COSMIIC-Inc/Implantables-Electrodes/Mechanical Design CAD Files/IM-MES Electrode Cable/SolidWorks Native Files/NNP-DWG-145-007-003 SA, Cable Body, Insulated SS Filars, Green-Clear.SLDASM

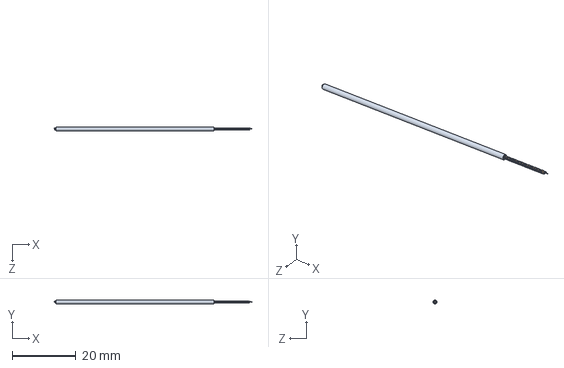
[picture p4: CAD file, 2024-06-29]
Mechanical Design CAD Files/IM-MES Electrode Cable/SolidWorks Native Files/NNP-DWG-145-007-003 SA, Cable Body, Insulated SS Filars, Green-Clear.SLDASM
62.2 x 1.27 x 1.27 mm
NNP-DWG-140-011-002 Filar, SS, Green-Clear
NNP-DWG-140-012-000 Cable, Insulating Silicone Tubing
