COSMIIC-Inc/Implantables-Electrodes/Mechanical Design CAD Files/IM Stim Electrode Cable/STEP Files/NNP-DWG-145-012-000 SA, Electrode, IM, Stim.STEP

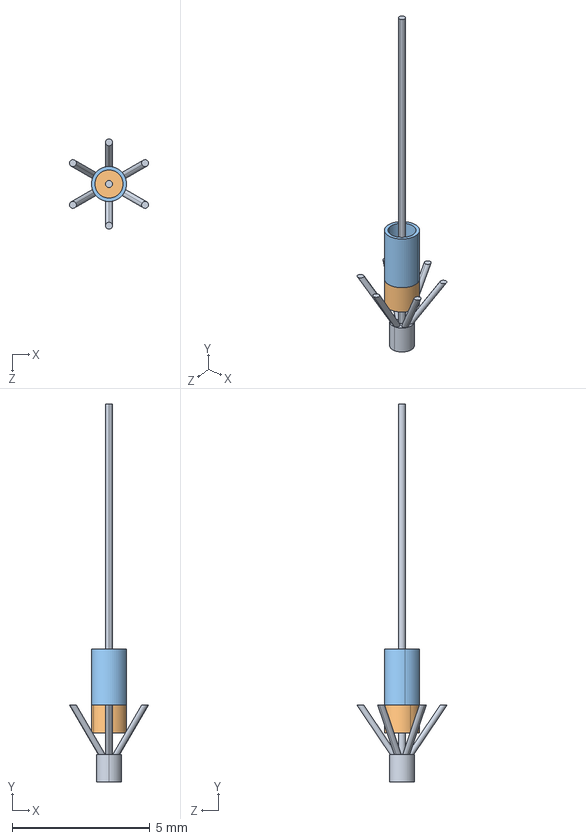
[picture p11: CAD file, 2024-07-09]
Mechanical Design CAD Files/IM Stim Electrode Cable/STEP Files/NNP-DWG-145-012-000 SA, Electrode, IM, Stim.STEP
2.87 x 13.7 x 3.28 mm
NNP-DWG-140-013-002 Electrode, IM, Stim, Prolene Barb
NNP-DWG-140-017-000 Electrode, IM, Silicone Tube Extension
NNP-DWG-140-019-002 Electrode, IM, Stim, Coil
