COSMIIC-Inc/Implantables-Electrodes/Mechanical Design CAD Files/IM-MES Electrode Cable/STEP Files/NNP-DWG-140-019-001 Electrode, IM, MES, Coil.STEP

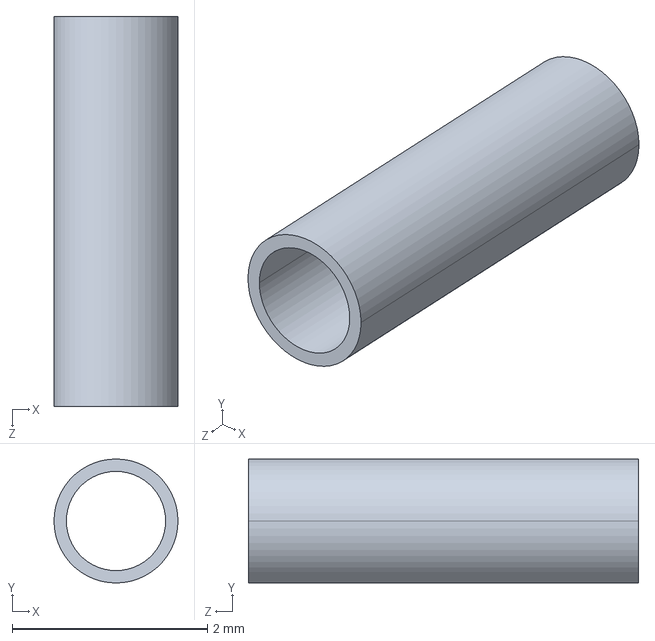
[picture p12: CAD file, 2024-07-09]
Mechanical Design CAD Files/IM-MES Electrode Cable/STEP Files/NNP-DWG-140-019-001 Electrode, IM, MES, Coil.STEP
1.27 x 1.27 x 4.00 mm
