COSMIIC-Inc/Implantables-Electrodes/Mechanical Design CAD Files/IM Stim Electrode Cable/STEP Files/NNP-DWG-140-012-000 Cable, Insulating Silicone Tubing.STEP

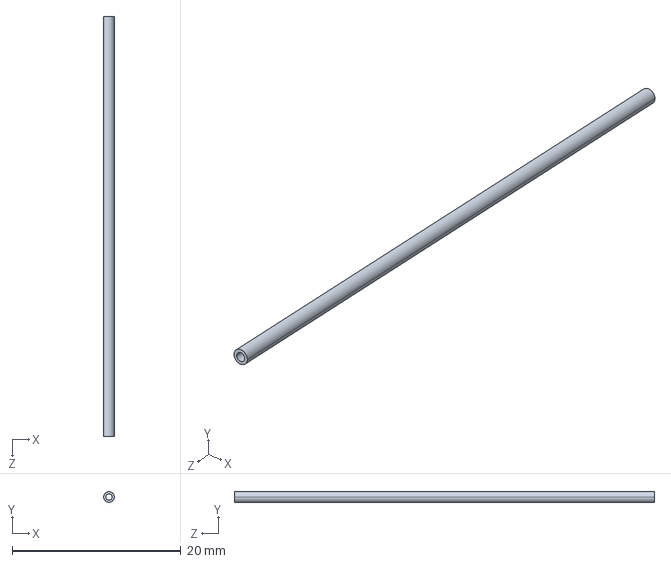
[picture p13: CAD file, 2024-06-29]
Mechanical Design CAD Files/IM Stim Electrode Cable/STEP Files/NNP-DWG-140-012-000 Cable, Insulating Silicone Tubing.STEP
1.27 x 1.27 x 49.8 mm
