COSMIIC-Inc/Implantables-Electrodes/Mechanical Design CAD Files/IM-MES Electrode Cable/STEP Files/NNP-DWG-145-011-000 SA, Electrode, IM, MES.STEP

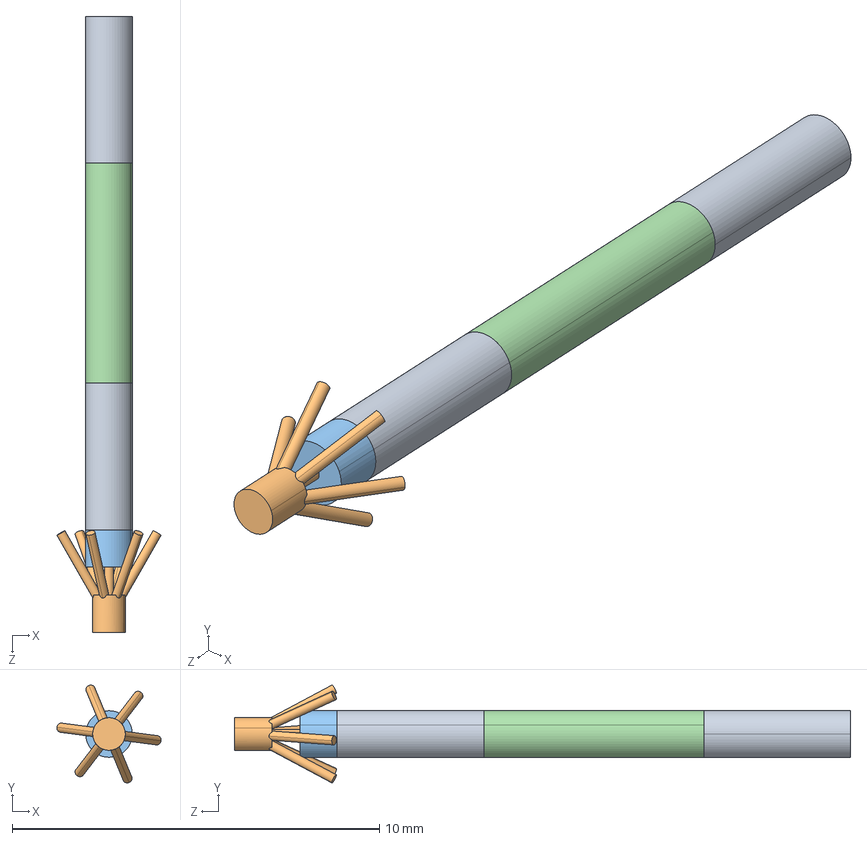
[picture p14: CAD file, 2024-07-09]
Mechanical Design CAD Files/IM-MES Electrode Cable/STEP Files/NNP-DWG-145-011-000 SA, Electrode, IM, MES.STEP
2.84 x 2.67 x 16.8 mm
NNP-DWG-140-019-000 Electrode, IM, Coil x 2
NNP-DWG-140-013-000 Electrode, IM, Prolene Barb
NNP-DWG-140-017-000 Electrode, IM, Silicone Tube Extension
NNP-DWG-140-018-000 Electrode, IM, Silicone Tubing Spacer
