COSMIIC-Inc/Implantables-Electrodes/Mechanical Design CAD Files/IM-MES Electrode Cable/SolidWorks Native Files/NNP-DWG-140-013-001 Electrode, IM, MES, Prolene Barb.SLDPRT

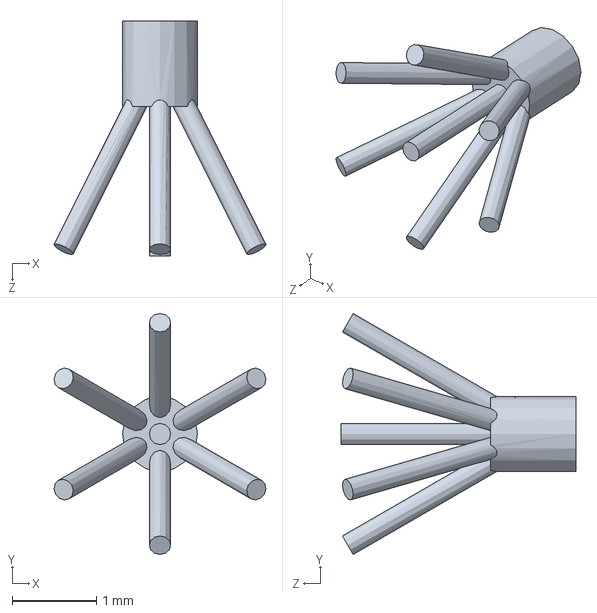
[picture p15: CAD file, 2024-07-09]
Mechanical Design CAD Files/IM-MES Electrode Cable/SolidWorks Native Files/NNP-DWG-140-013-001 Electrode, IM, MES, Prolene Barb.SLDPRT
2.52 x 2.86 x 2.79 mm
