COSMIIC-Inc/Implantables-Electrodes/Mechanical Design CAD Files/IM-MES Electrode Cable/STEP Files/NNP-DWG-145-001-000 Interconnect.STEP

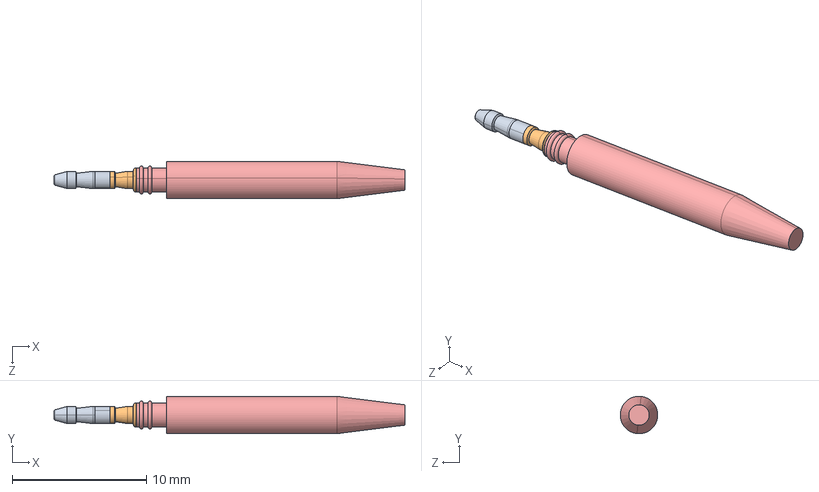
[picture p16: CAD file, 2024-06-29]
Mechanical Design CAD Files/IM-MES Electrode Cable/STEP Files/NNP-DWG-145-001-000 Interconnect.STEP
26.2 x 2.79 x 2.79 mm
NNP-DWG-140-004-000 Interconnect, Front-Rear Insulator
NNP-DWG-140-002-001 Interconnect, Rear Contact, SS
NNP-DWG-140-007-001 Interconnect, Front Weld Sleeve, SS
NNP-DWG-140-008-001 Interconnect, Crimp Weld Reducer, SS
NNP-DWG-140-009-000 Interconnect, Silicone Over Mold
NNP-DWG-140-003-001 Interconnect, NNP Center Conductor, SS
NNP-DWG-140-006-000 Interconnect, Washer
NNP-DWG-140-005-001 Interconnect, Strain Relief, SS
NNP-DWG-140-001-001 Interconnect, Front Contact, SS
