COSMIIC-Inc/Implantables-Electrodes/Mechanical Design CAD Files/IM Stim Electrode Cable/SolidWorks Native Files/NNP-DWG-140-017-000 Electrode, IM, Silicone Tube Extension.SLDPRT

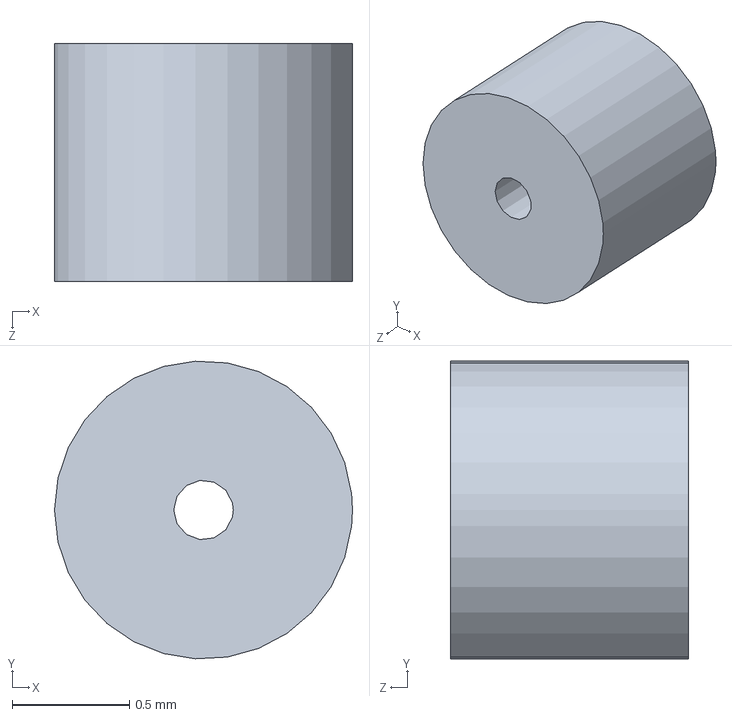
[picture p17: CAD file, 2024-07-09]
Mechanical Design CAD Files/IM Stim Electrode Cable/SolidWorks Native Files/NNP-DWG-140-017-000 Electrode, IM, Silicone Tube Extension.SLDPRT
1.27 x 1.27 x 1.02 mm
