COSMIIC-Inc/Implantables-Electrodes/Mechanical Design CAD Files/IM-MES Electrode Cable/SolidWorks Native Files/NNP-DWG-140-011-002 Filar, SS, Green-Clear.SLDPRT

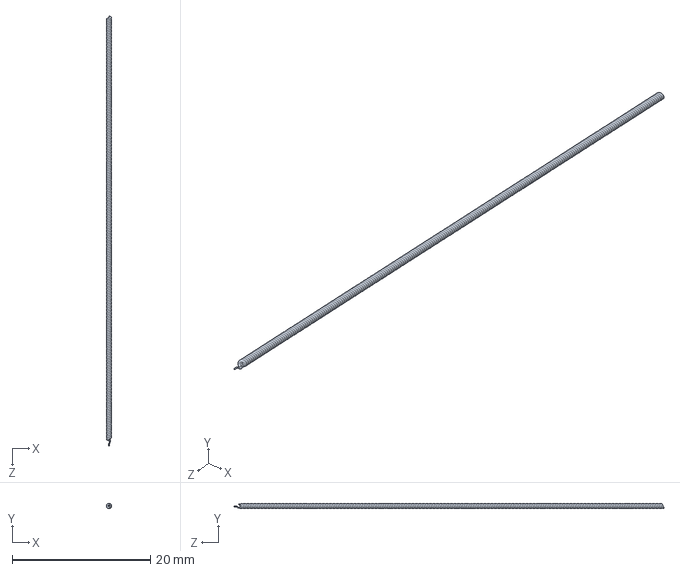
[picture p19: CAD file, 2024-06-29]
Mechanical Design CAD Files/IM-MES Electrode Cable/SolidWorks Native Files/NNP-DWG-140-011-002 Filar, SS, Green-Clear.SLDPRT
0.762 x 0.762 x 62.2 mm
