COSMIIC-Inc/Implantables-Electrodes/Mechanical Design CAD Files/IM Stim Electrode Cable/Drawing PDFs/NNP-DWG-145-005-000 Electrode Cable, IM, Stim.pdf

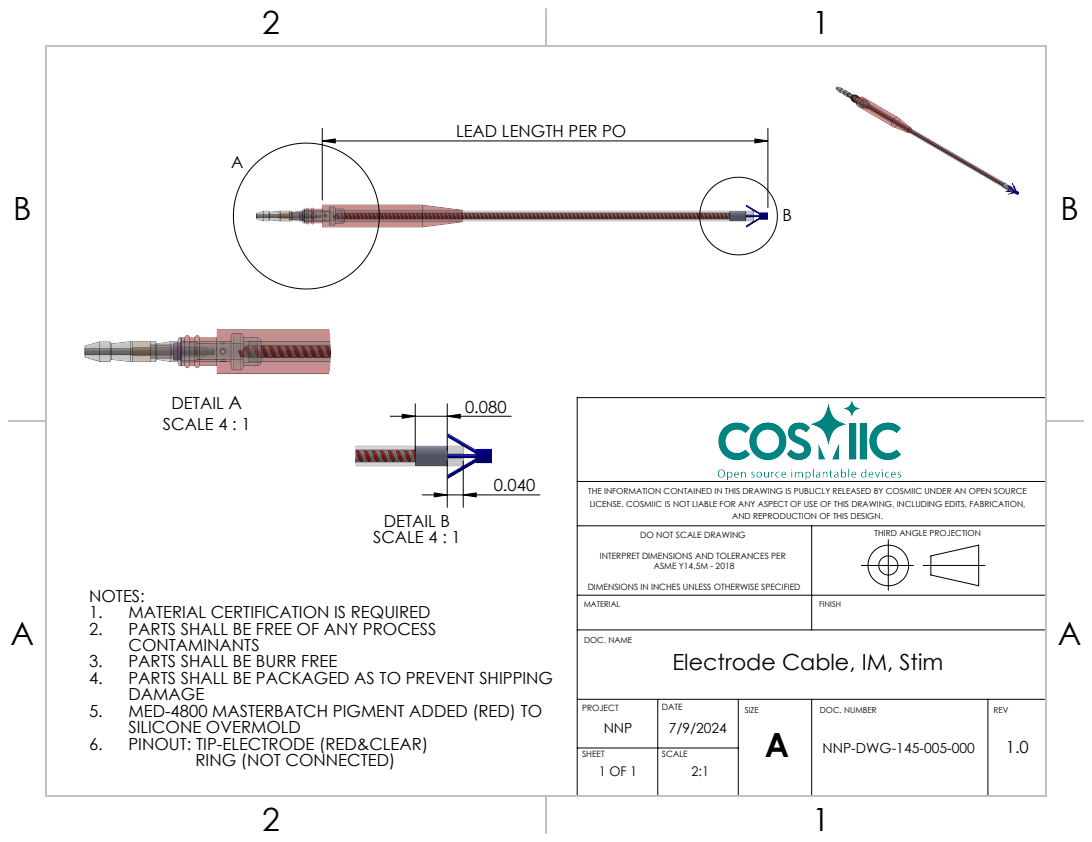
[picture p28: page 1]
DETAIL A SCALE 4 : 1; DETAIL B SCALE 4 : 1; ASME Y14.5M - 2018; DOC. NAME; DOC. NUMBER; REV

LEAD LENGTH PER PO

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

AND REPRODUCTION OF THIS DESIGN.

DO NOT SCALE DRAWING

THIRD ANGLE PROJECTION

INTERPRET DIMENSIONS AND TOLERANCES PER

NOTES:
1. MATERIAL CERTIFICATION IS REQUIRED

DIMENSIONS IN INCHES UNLESS OTHERWISE SPECIFIED
Electrode Cable, IM, Stim

2. PARTS SHALL BE FREE OF ANY PROCESS
CONTAMINANTS
3. PARTS SHALL BE BURR FREE
4. PARTS SHALL BE PACKAGED AS TO PREVENT SHIPPING
DAMAGE
5. MED-4800 MASTERBATCH PIGMENT ADDED (RED) TO
SILICONE OVERMOLD
6. PINOUT: TIP-ELECTRODE (RED&CLEAR)

RING (NOT CONNECTED)
