COSMIIC-Inc/Implantables-Electrodes/Mechanical Design CAD Files/IM Stim Electrode Cable/Drawing PDFs/NNP-DWG-145-007-002 SA, Cable Body, Insulated SS Filars, Red-Clear.pdf

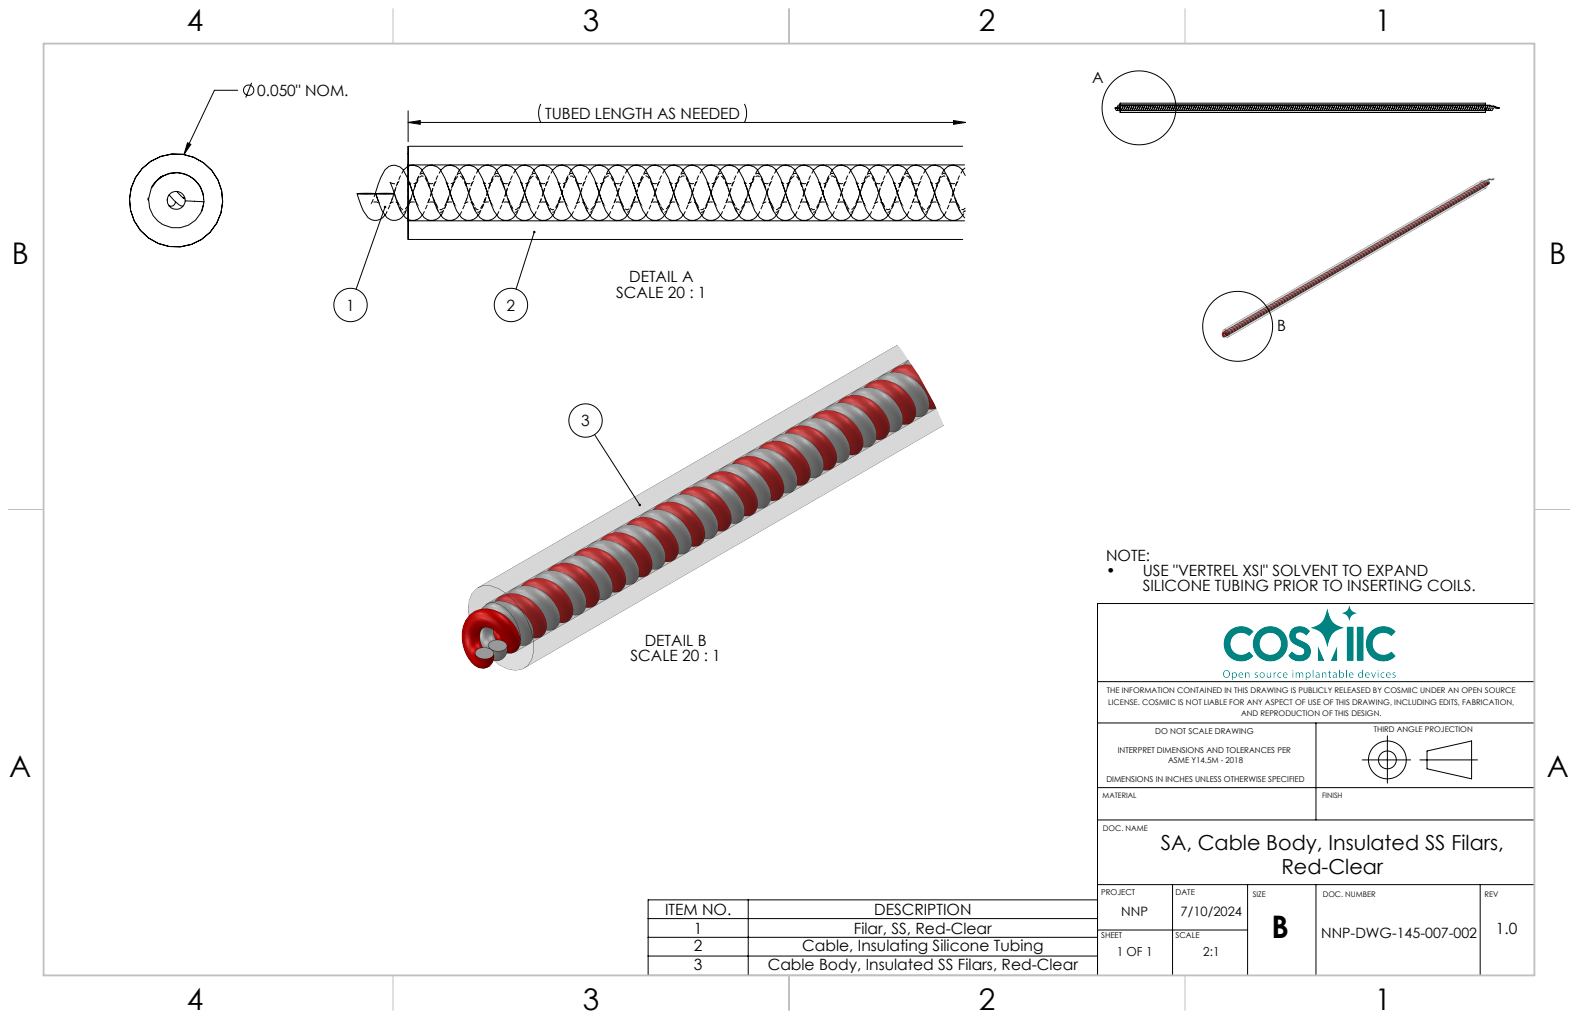
[picture p29: page 1]
0.050" NOM.; DETAIL A SCALE 20 : 1; DETAIL B SCALE 20 : 1; DOC. NUMBER; REV; DOC. NAME; ASME Y14.5M - 2018

TUBED LENGTH AS NEEDED

NOTE:
• USE "VERTREL XSI" SOLVENT TO EXPAND
SILICONE TUBING PRIOR TO INSERTING COILS.

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

AND REPRODUCTION OF THIS DESIGN.

DO NOT SCALE DRAWING

THIRD ANGLE PROJECTION

INTERPRET DIMENSIONS AND TOLERANCES PER

DIMENSIONS IN INCHES UNLESS OTHERWISE SPECIFIED
SA, Cable Body, Insulated SS Filars,
NNP-DWG-145-007-002

ITEM NO. | DESCRIPTION
1 | Filar, SS, Red-Clear
2 | Cable, Insulating Silicone Tubing
3 | Cable Body, Insulated SS Filars, Red-Clear
