COSMIIC-Inc/Implantables-Electrodes/Mechanical Design CAD Files/Epimysial MES Electrode Cable/Drawing PDFs/NNP-DWG-140-015-000 Electrode, EPI, MES, Silicone Molding Blank.pdf

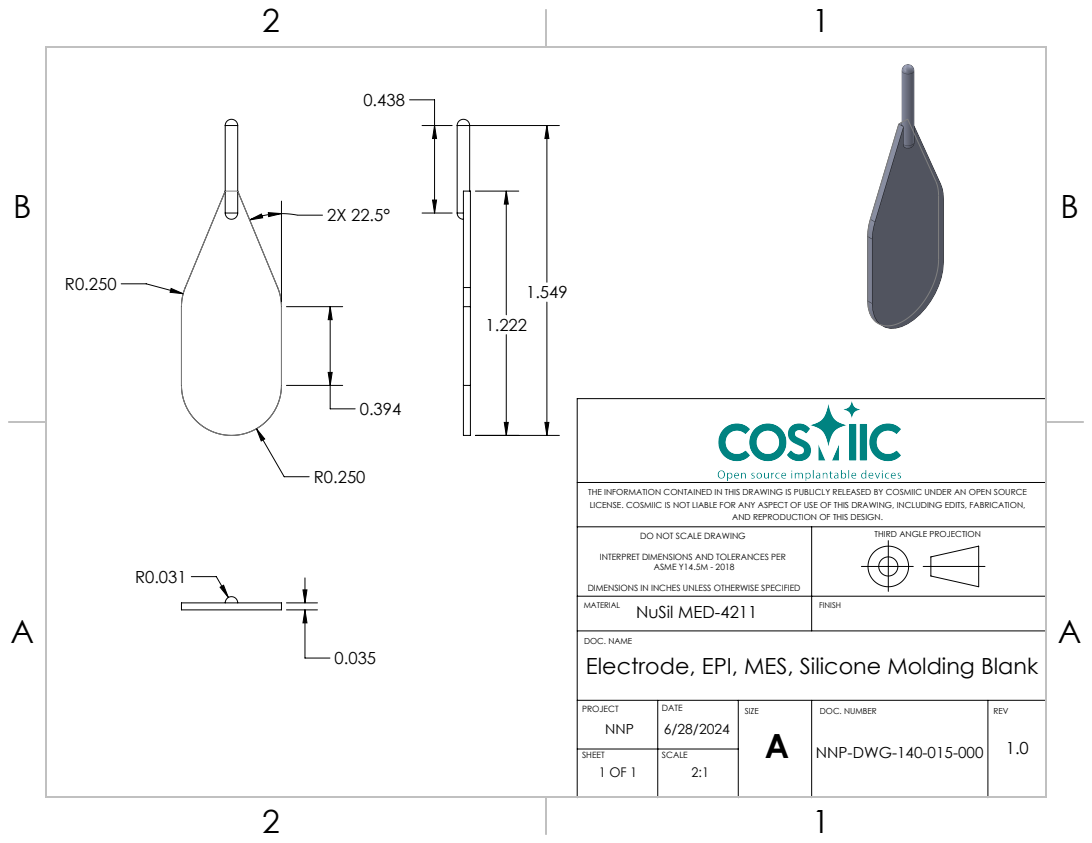
[picture p30: page 1]
NNP-DWG-140-015-000 1.0; DOC. NAME; DOC. NUMBER; REV

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

AND REPRODUCTION OF THIS DESIGN.

DO NOT SCALE DRAWING

THIRD ANGLE PROJECTION

INTERPRET DIMENSIONS AND TOLERANCES PER

ASME Y14.5M - 2018
NuSil MED-4211
Electrode, EPI, MES, Silicone Molding Blank

DIMENSIONS IN INCHES UNLESS OTHERWISE SPECIFIED
