COSMIIC-Inc/Implantables-Electrodes/Mechanical Design CAD Files/IM Stim Electrode Cable/Drawing PDFs/NNP-DWG-140-012-000 Cable, Insulating Silicone Tubing.pdf

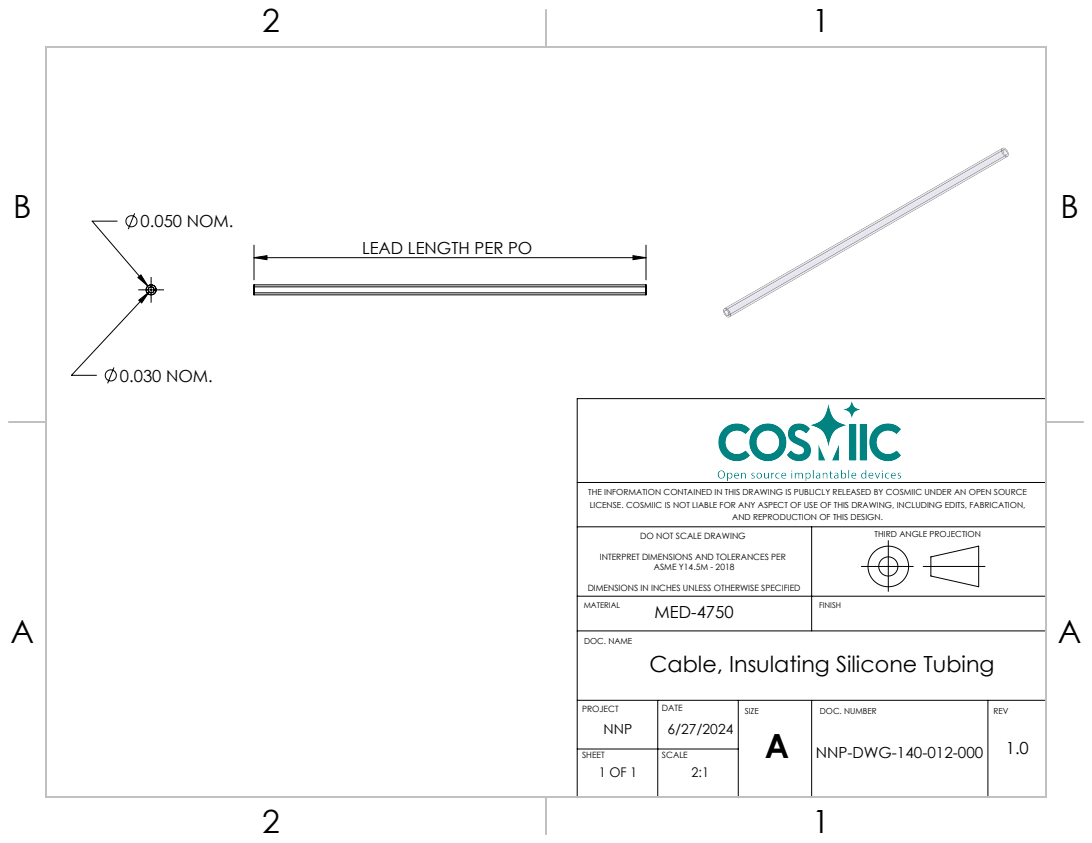
[picture p31: page 1]
0.050 NOM.; 0.030 NOM.; NNP-DWG-140-012-000 1.0; ASME Y14.5M - 2018; DOC. NAME; DOC. NUMBER; REV; Cable, Insulating Silicone Tubing

LEAD LENGTH PER PO

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

AND REPRODUCTION OF THIS DESIGN.

DO NOT SCALE DRAWING

THIRD ANGLE PROJECTION

INTERPRET DIMENSIONS AND TOLERANCES PER

DIMENSIONS IN INCHES UNLESS OTHERWISE SPECIFIED
